biancapintilie/TSC-OpenBook/Images/exploded_view.png

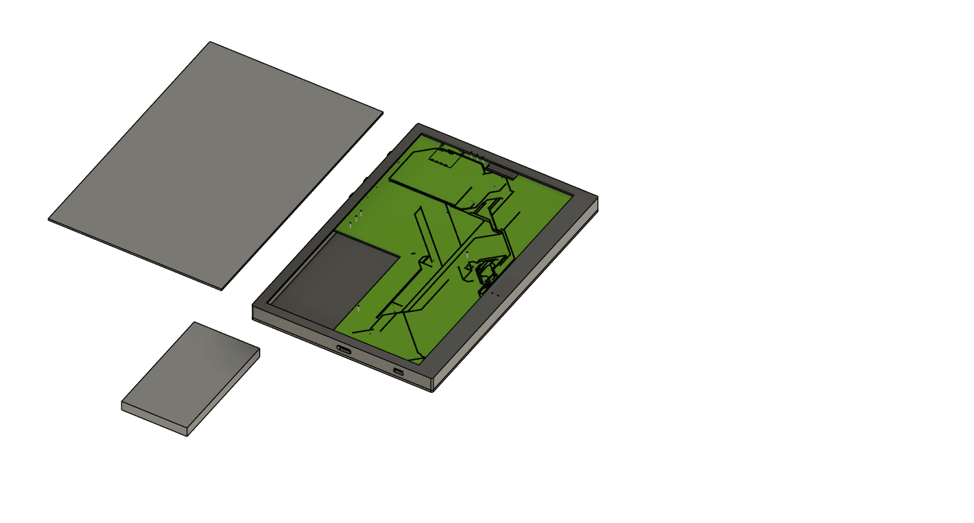
Images/exploded_view.png
