biancapintilie/TSC-OpenBook/Images/openbook_pcb.jpg

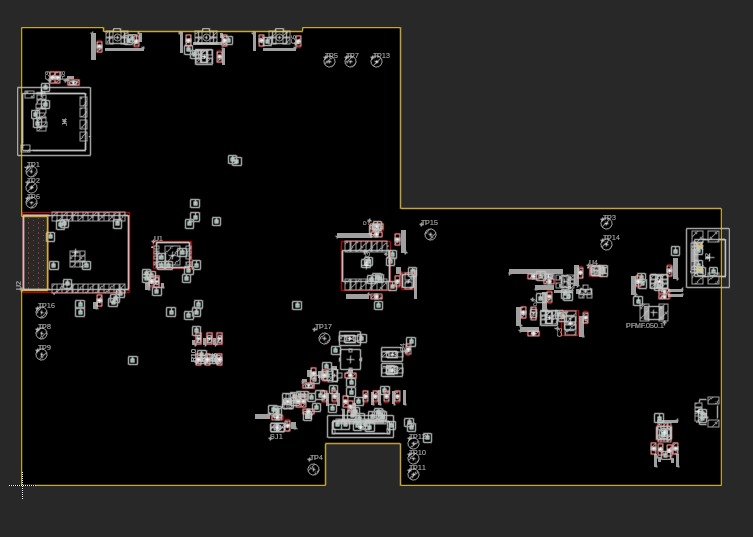
Images/openbook_pcb.jpg
