biancapintilie/TSC-OpenBook/Images/schema bloc.png

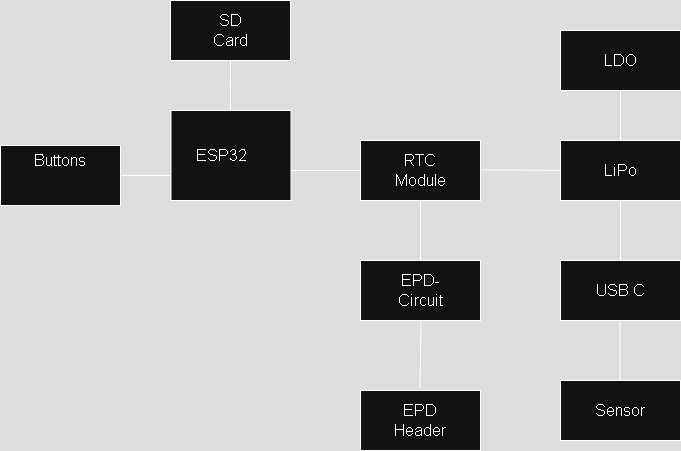
Images/schema bloc.png
